SparksEngineer/Alternate-Switch-Control-Interface-Device/Send_BatteryVoltageMsg-BLE/Send_BatteryVoltageMsg-BLE.ino

#include <Arduino.h>
#include <SPI.h>
#include "Adafruit_BLE.h"
#include "Adafruit_BluefruitLE_SPI.h"
#include "Adafruit_BluefruitLE_UART.h"

#include "BluefruitConfig.h"

#if SOFTWARE_SERIAL_AVAILABLE
#include <SoftwareSerial.h>
#endif

#define FACTORYRESET_ENABLE         1
#define MINIMUM_FIRMWARE_VERSION    "0.6.6"
#define MODE_LED_BEHAVIOUR          "MODE"

Adafruit_BluefruitLE_SPI ble(BLUEFRUIT_SPI_CS, BLUEFRUIT_SPI_IRQ, BLUEFRUIT_SPI_RST);

void error(const __FlashStringHelper*err) {
  Serial.println(err);
  while (1);
}
/**In the the Feather32u4 A1=D19, and in the Feather M0 A1=D15**/
const int GreenLED = 15;//GREEN LED connected to pin A1
const int RedLED = 16;//RED LED connected to pin A2
const int VBATPIN = 9;//Vatpin is A7 or D9 for Feather 32u4

void setup() {
  // put your setup code here, to run once:

  Serial.begin(115200);
  Serial.println(F("Adafruit Bluefruit Command <-> Data Mode Example"));
  Serial.println(F("------------------------------------------------"));

  /* Initialise the module */
  Serial.print(F("Initialising the Bluefruit LE module: "));

  if ( !ble.begin(VERBOSE_MODE) )
  {
    error(F("Couldn't find Bluefruit, make sure it's in CoMmanD mode & check wiring?"));
  }
  Serial.println( F("OK!") );

  if ( FACTORYRESET_ENABLE )
  {
    /* Perform a factory reset to make sure everything is in a known state */
    Serial.println(F("Performing a factory reset: "));
    if ( ! ble.factoryReset() ) {
      error(F("Couldn't factory reset"));
    }
  }

  /* Disable command echo from Bluefruit */
  ble.echo(false);

  Serial.println("Requesting Bluefruit info:");
  /* Print Bluefruit information */
  ble.info();

  Serial.println(F("Please use Adafruit Bluefruit LE app to connect in UART mode"));
  Serial.println(F("Then Enter characters to send to Bluefruit"));
  Serial.println();

  ble.verbose(false);  // debug info is a little annoying after this point!

  /* Wait for connection */
  while (! ble.isConnected()) {
    delay(500);
  }

  Serial.println(F("******************************"));

  // LED Activity command is only supported from 0.6.6
  if ( ble.isVersionAtLeast(MINIMUM_FIRMWARE_VERSION) )
  {
    // Change Mode LED Activity
    Serial.println(F("Change LED activity to " MODE_LED_BEHAVIOUR));
    ble.sendCommandCheckOK("AT+HWModeLED=" MODE_LED_BEHAVIOUR);
  }

  // Set module to DATA mode
  Serial.println( F("Switching to DATA mode!") );
  ble.setMode(BLUEFRUIT_MODE_DATA);

  Serial.println(F("******************************"));
  pinMode(VBATPIN, INPUT);
  pinMode(GreenLED, OUTPUT);//declare LED as output
  pinMode(RedLED, OUTPUT);
}

void loop() {
  // put your main code here, to run repeatedly:
  float measuredvbat = analogRead(VBATPIN);
  measuredvbat *= 2;    // we divided by 2, so multiply back
  measuredvbat *= 3.3;  // Multiply by 3.3V, our reference voltage
  measuredvbat /= 1024; // convert to voltage

  //Print Battery voltage bvalue to Serial Monitor
  Serial.print("VBat: " ); Serial.println(measuredvbat);

  // Send characters to Bluefruit
  Serial.print("Sending: ");

  //Send input data to host via Bluefruit
  ble.println(measuredvbat);
  delay(2000);
}
